dtbinh/AntRobots_2.0/CAD_files/ArduinoMega.SLDPRT

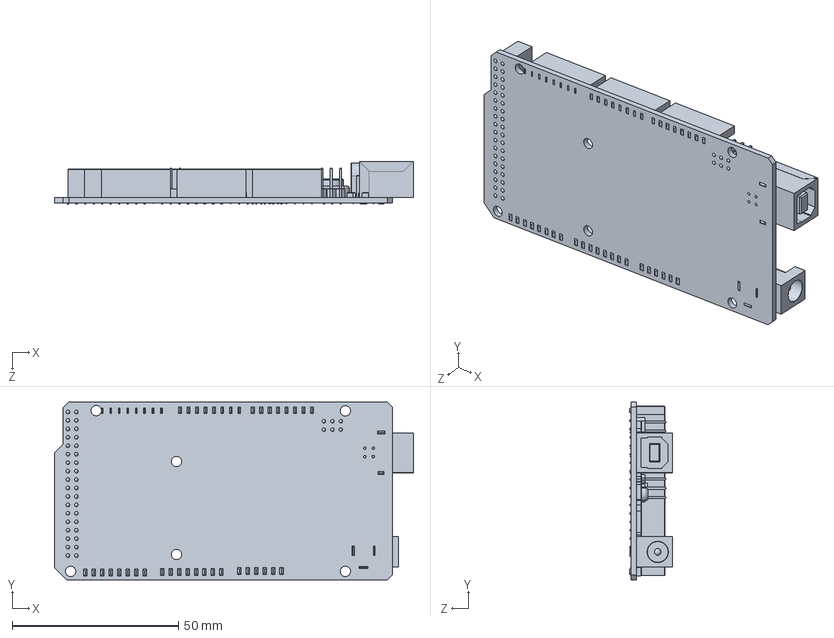
[picture p15: CAD file, 2016-06-14]
CAD_files/ArduinoMega.SLDPRT
107.9 x 53.4 x 13.0 mm
