dtbinh/AntRobots_2.0/CAD_files/micro claw base.SLDPRT

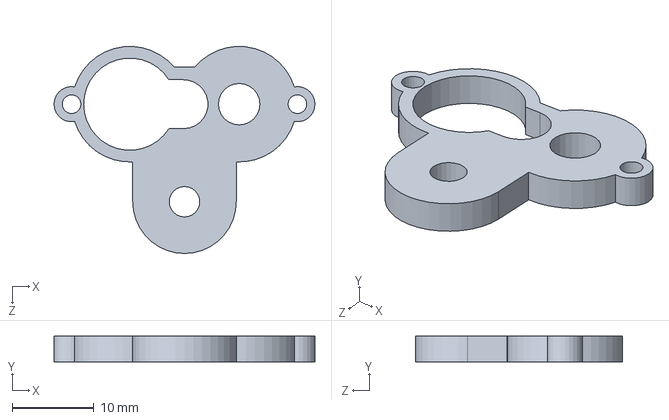
[picture p16: CAD file, 2016-06-14]
CAD_files/micro claw base.SLDPRT
32.0 x 3.17 x 25.4 mm
