dtbinh/AntRobots_2.0/CAD_files/new_ee_holder.SLDPRT

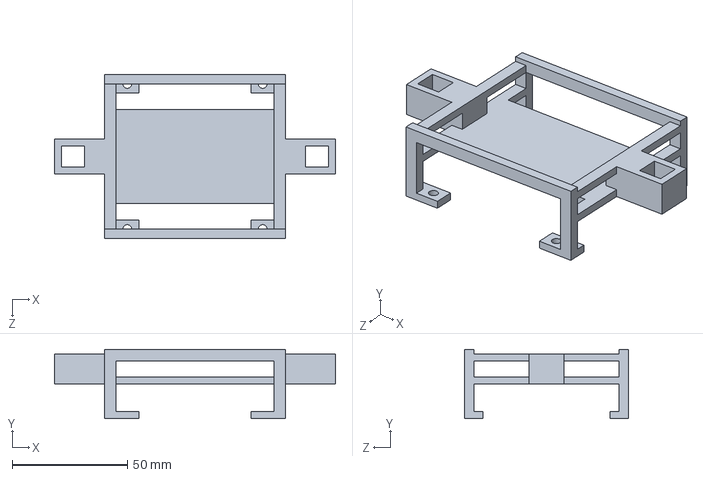
[picture p17: CAD file, 2016-06-14]
CAD_files/new_ee_holder.SLDPRT
122.0 x 30.0 x 71.0 mm
