dtbinh/AntRobots_2.0/CAD_files/pixy_lens.SLDPRT

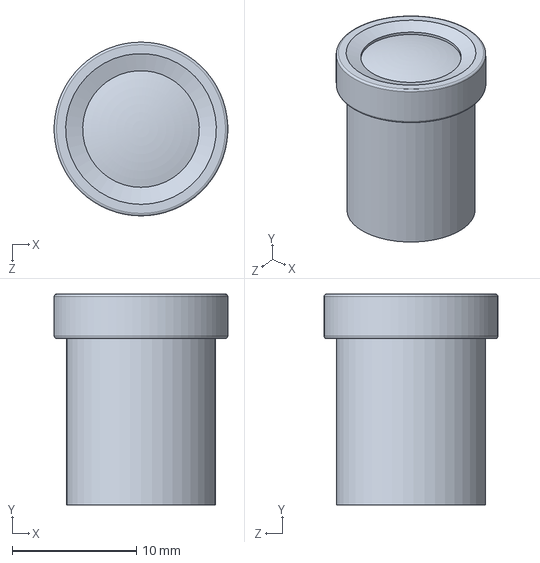
[picture p18: CAD file, 2016-06-14]
CAD_files/pixy_lens.SLDPRT
14.0 x 17.0 x 14.0 mm
