dtbinh/AntRobots_2.0/CAD_files/front mount.SLDPRT

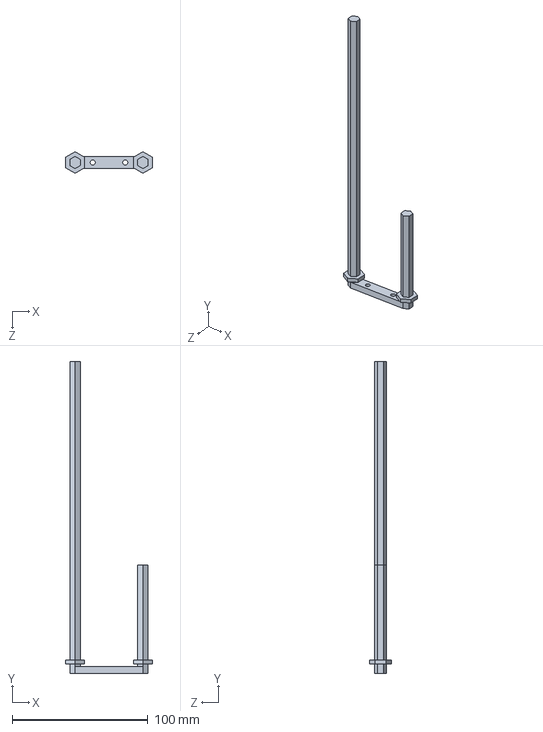
[picture p19: CAD file, 2016-06-14]
CAD_files/front mount.SLDPRT
63.8 x 230.0 x 15.9 mm
