dtbinh/AntRobots_2.0/CAD_files/front caster holder.SLDPRT

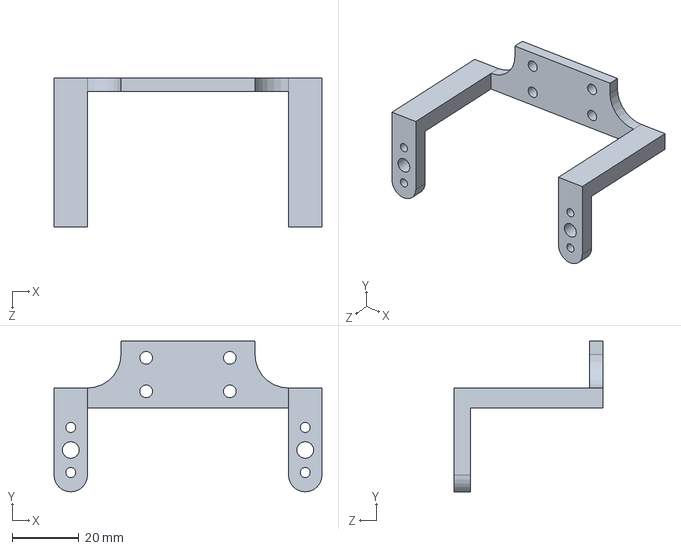
[picture p20: CAD file, 2016-06-14]
CAD_files/front caster holder.SLDPRT
80.0 x 45.0 x 44.5 mm
