dtbinh/AntRobots_2.0/CAD_files/switch-FSMRA6JH.SLDPRT

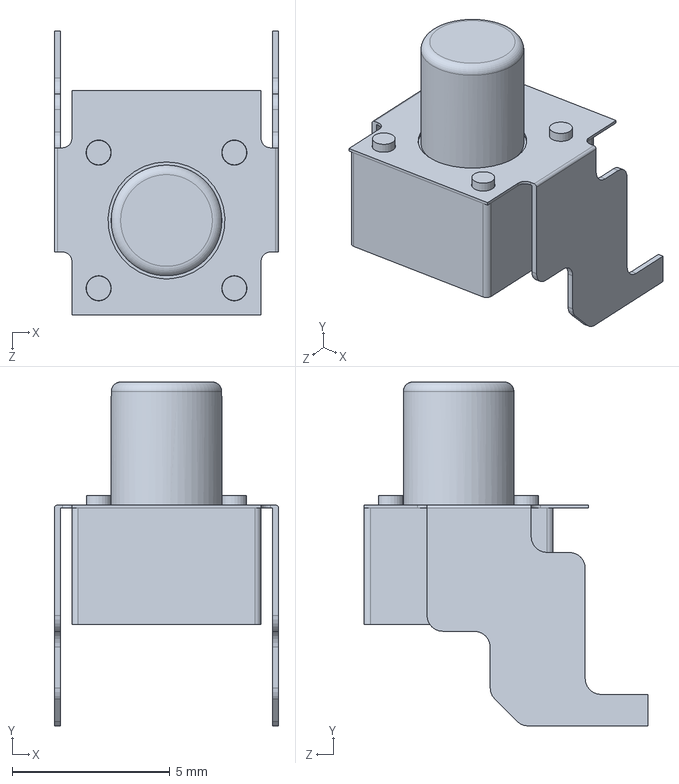
[picture p21: CAD file, 2016-06-14]
CAD_files/switch-FSMRA6JH.SLDPRT
7.11 x 10.9 x 8.99 mm
