dtbinh/AntRobots_2.0/CAD_files/Metal Ball Caster.SLDPRT

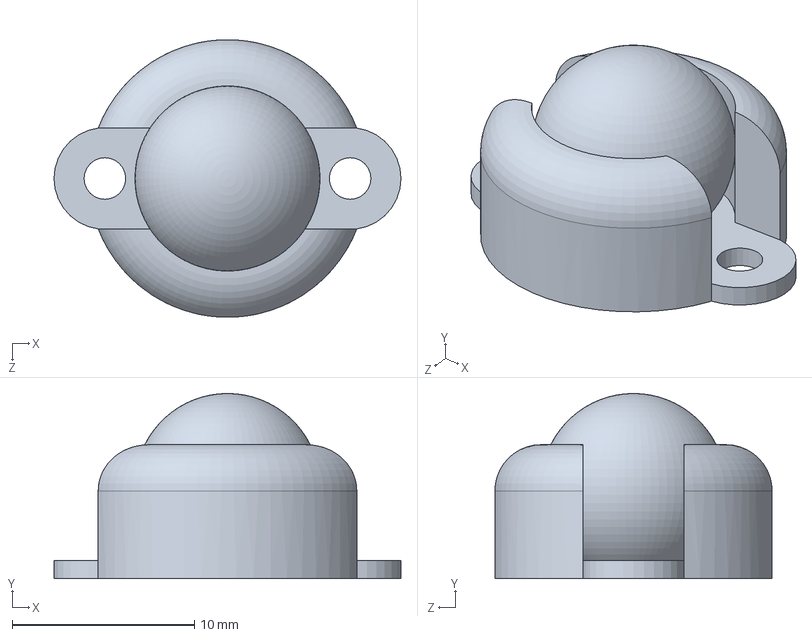
[picture p22: CAD file, 2016-06-14]
CAD_files/Metal Ball Caster.SLDPRT
19.1 x 10.2 x 15.2 mm
