dtbinh/AntRobots_2.0/CAD_files/Pixy_board.SLDPRT

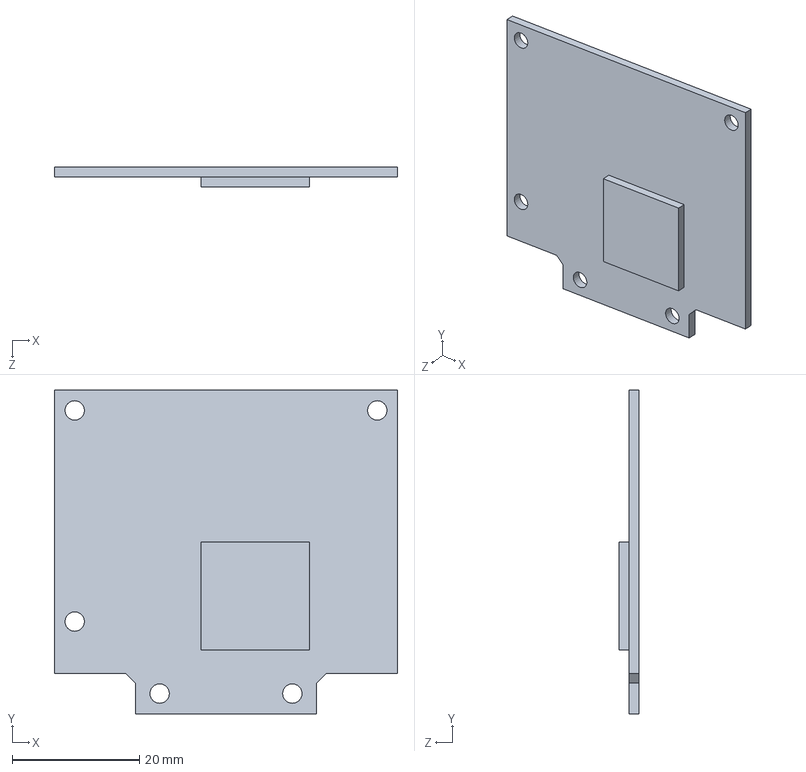
[picture p23: CAD file, 2016-06-14]
CAD_files/Pixy_board.SLDPRT
53.8 x 50.8 x 3.20 mm
