dtbinh/AntRobots_2.0/CAD_files/elecHolder.SLDPRT

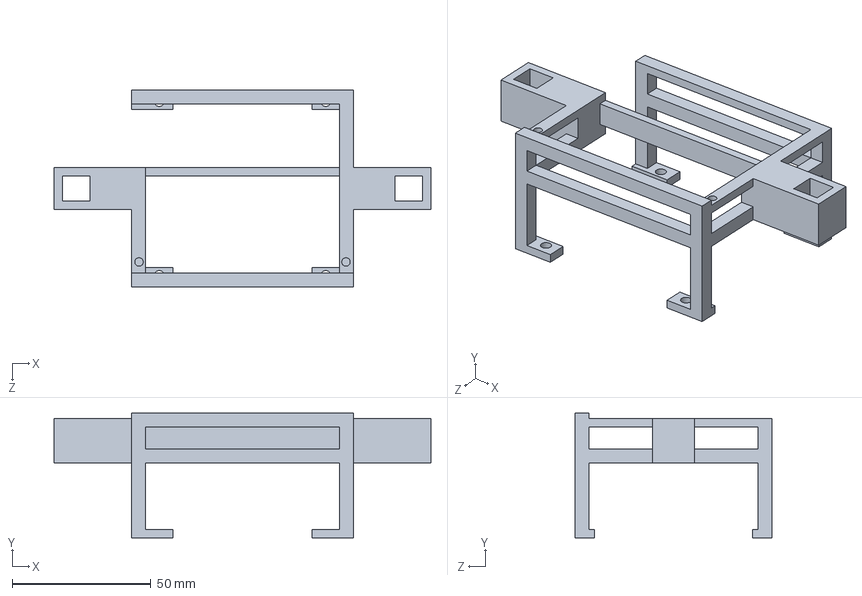
[picture p24: CAD file, 2016-06-14]
CAD_files/elecHolder.SLDPRT
136.0 x 45.0 x 71.0 mm
