dtbinh/AntRobots_2.0/CAD_files/Part2.SLDPRT

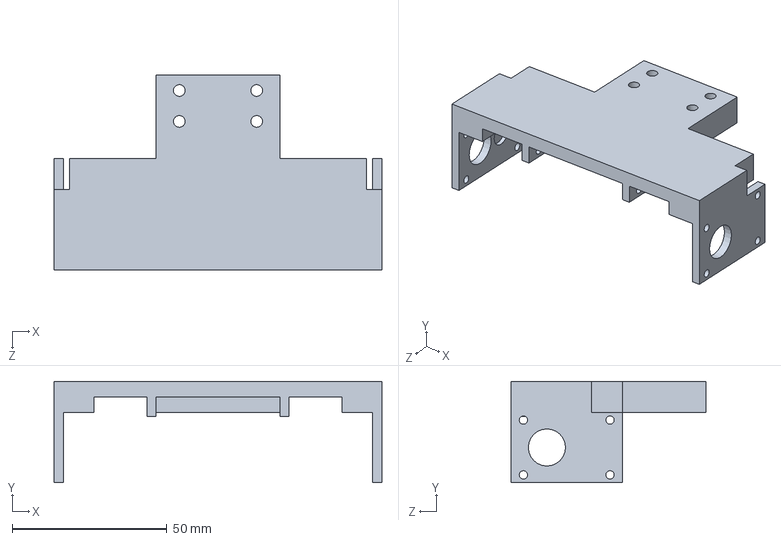
[picture p25: CAD file, 2016-06-14]
CAD_files/Part2.SLDPRT
106.0 x 32.6 x 63.0 mm
