dtbinh/AntRobots_2.0/CAD_files/M12_lens_holder.SLDPRT

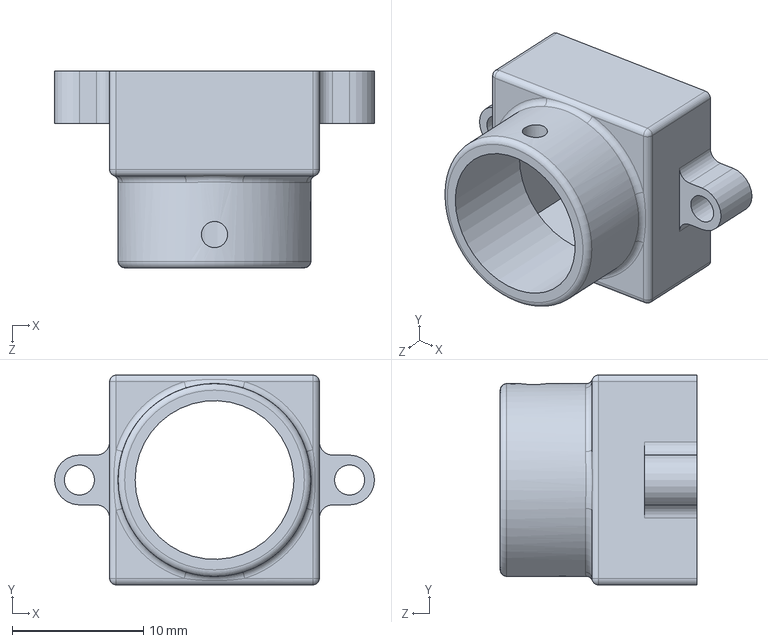
[picture p26: CAD file, 2016-06-14]
CAD_files/M12_lens_holder.SLDPRT
24.4 x 16.0 x 15.0 mm
