dtbinh/AntRobots_2.0/CAD_files/new side adapter.SLDPRT

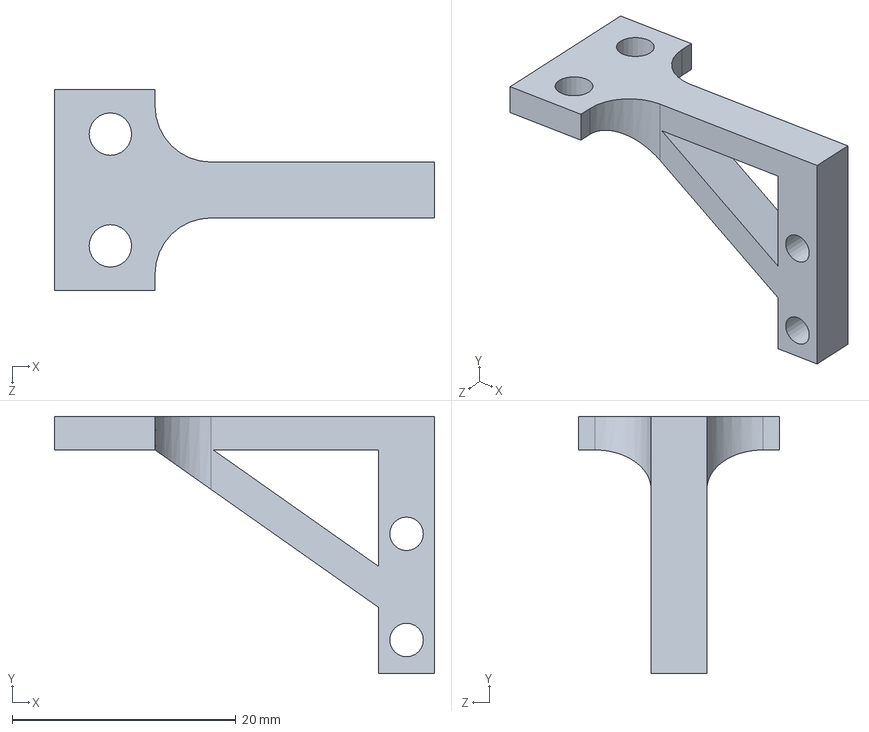
[picture p27: CAD file, 2016-06-14]
CAD_files/new side adapter.SLDPRT
34.0 x 23.0 x 18.0 mm
