dtbinh/AntRobots_2.0/CAD_files/claw.SLDPRT

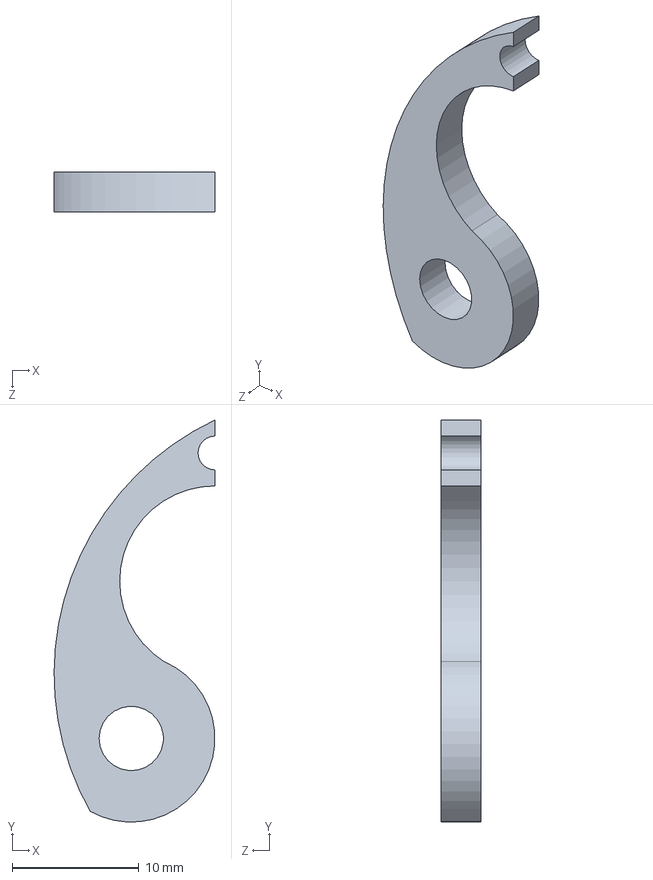
[picture p28: CAD file, 2016-06-14]
CAD_files/claw.SLDPRT
12.7 x 31.7 x 3.17 mm
