dtbinh/AntRobots_2.0/CAD_files/whisker mount.SLDPRT

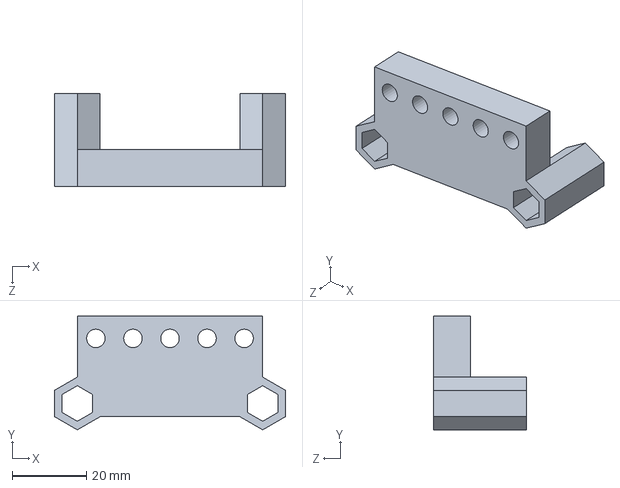
[picture p29: CAD file, 2016-06-14]
CAD_files/whisker mount.SLDPRT
62.3 x 30.7 x 25.0 mm
