dtbinh/AntRobots_2.0/CAD_files/header_MTA-100_2pins.SLDPRT

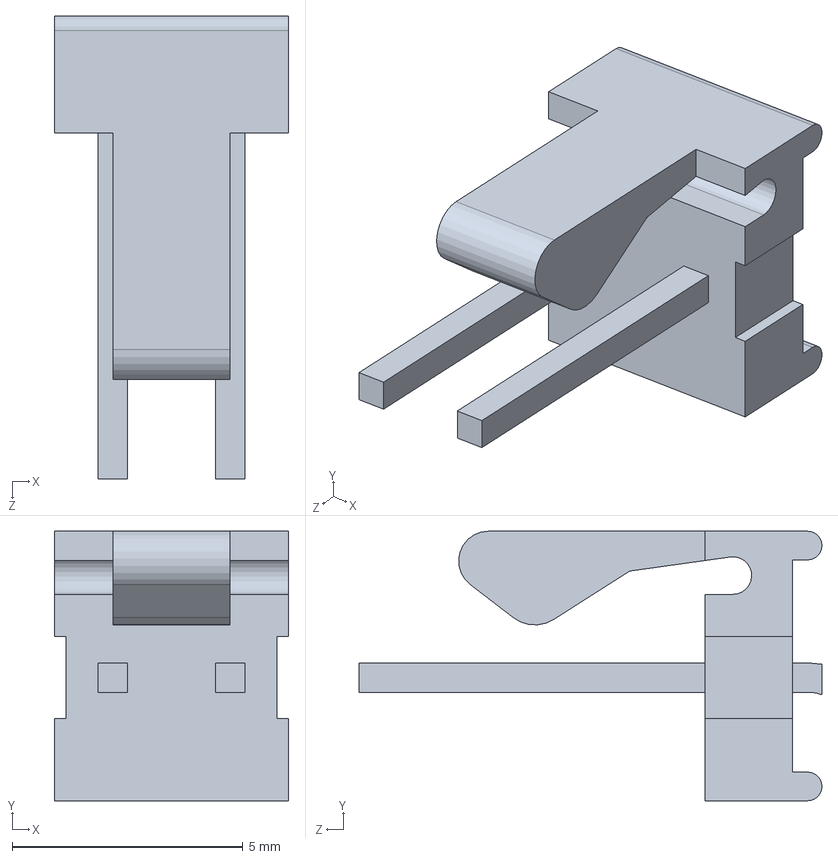
[picture p30: CAD file, 2016-06-14]
CAD_files/header_MTA-100_2pins.SLDPRT
5.08 x 5.84 x 10.0 mm
