dtbinh/AntRobots_2.0/CAD_files/ModularBodyBase.SLDPRT

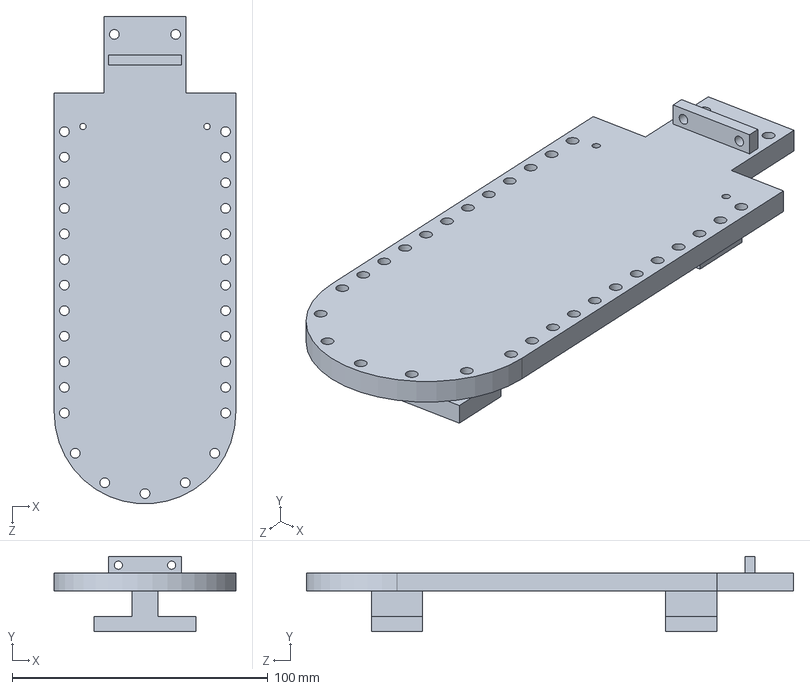
[picture p31: CAD file, 2016-06-14]
CAD_files/ModularBodyBase.SLDPRT
71.0 x 29.5 x 190.4 mm
