dtbinh/AntRobots_2.0/CAD_files/head mount spacer.SLDPRT

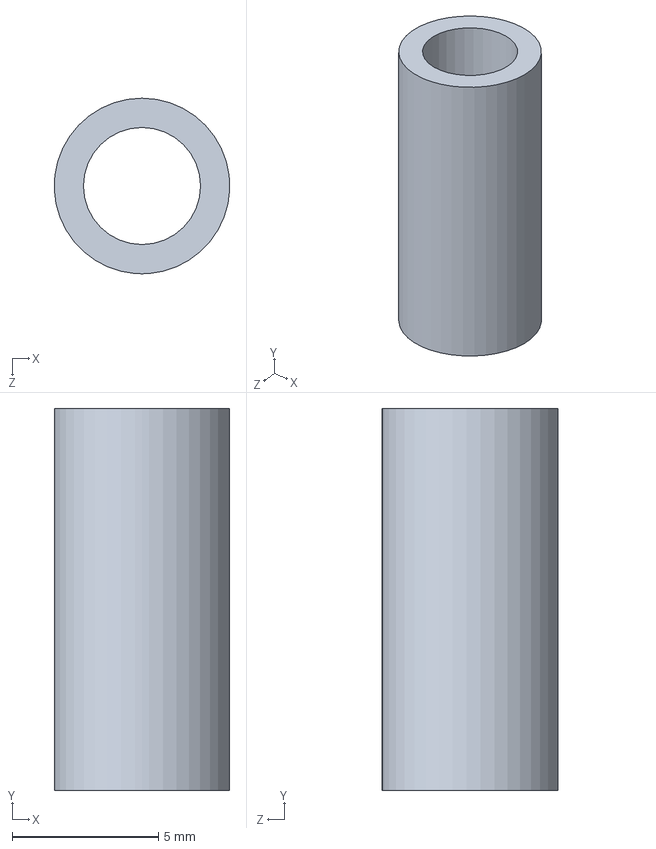
[picture p32: CAD file, 2016-06-14]
CAD_files/head mount spacer.SLDPRT
6.00 x 13.1 x 6.00 mm
