dtbinh/AntRobots_2.0/CAD_files/arm mount.SLDPRT

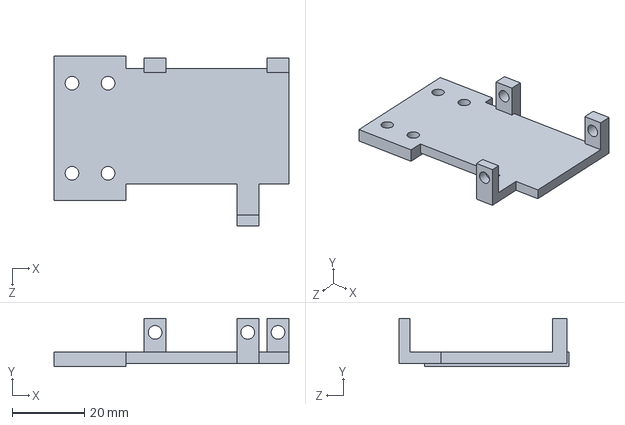
[picture p33: CAD file, 2016-06-14]
CAD_files/arm mount.SLDPRT
65.2 x 13.4 x 47.1 mm
