dtbinh/AntRobots_2.0/CAD_files/dummy battery.SLDPRT

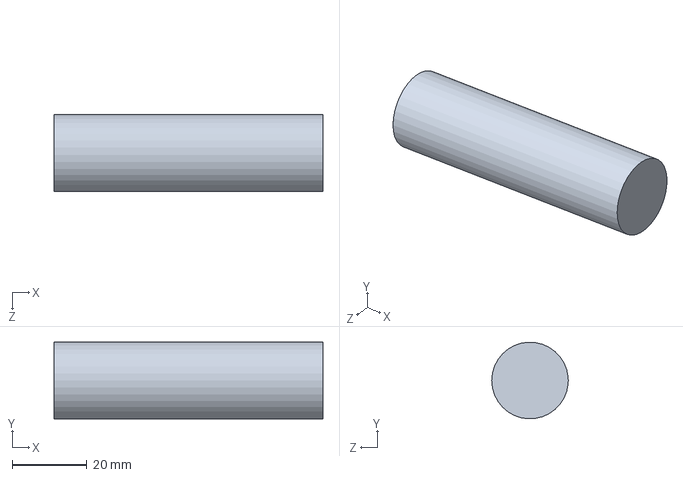
[picture p34: CAD file, 2016-06-14]
CAD_files/dummy battery.SLDPRT
72.0 x 20.5 x 20.5 mm
