dtbinh/AntRobots_2.0/CAD_files/quickIMU.SLDPRT

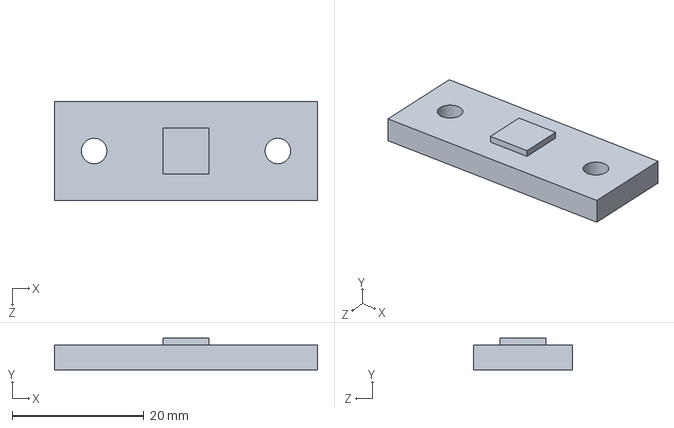
[picture p35: CAD file, 2016-06-14]
CAD_files/quickIMU.SLDPRT
40.0 x 4.80 x 15.0 mm
