dtbinh/AntRobots_2.0/CAD_files/batHolder.SLDPRT

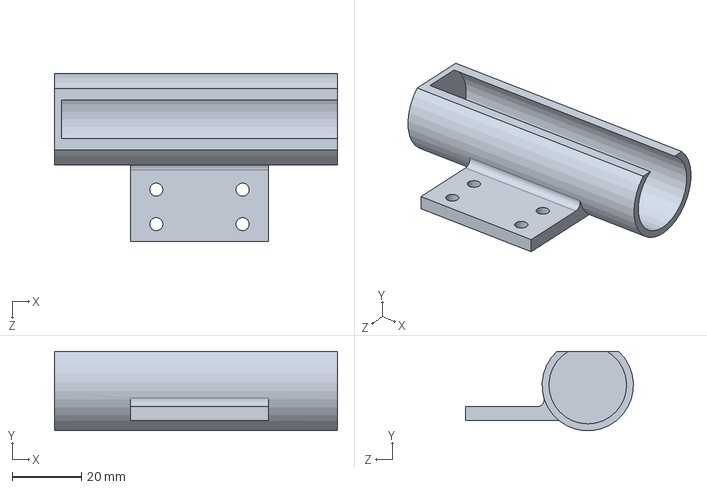
[picture p36: CAD file, 2016-06-14]
CAD_files/batHolder.SLDPRT
82.0 x 22.9 x 48.6 mm
