dtbinh/AntRobots_2.0/CAD_files/quick_switch.SLDPRT

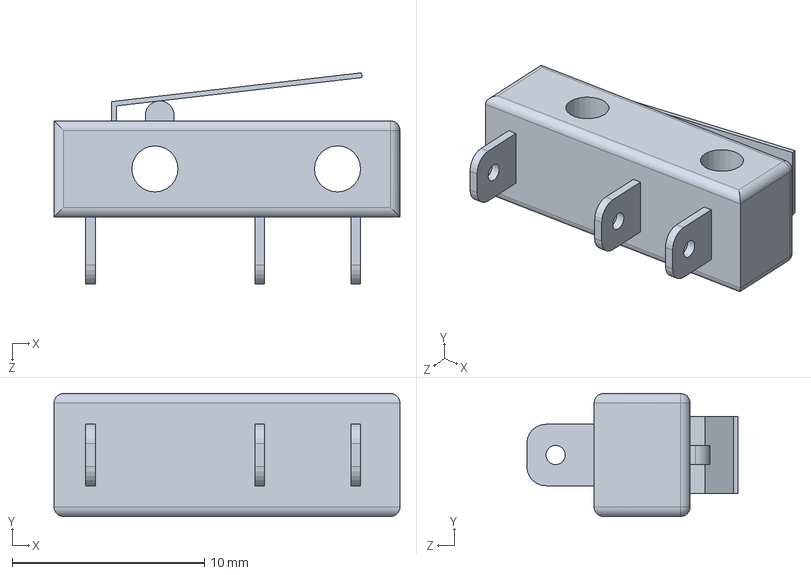
[picture p37: CAD file, 2016-06-14]
CAD_files/quick_switch.SLDPRT
18.0 x 6.40 x 11.0 mm
