dtbinh/AntRobots_2.0/CAD_files/IR Sensor.SLDPRT

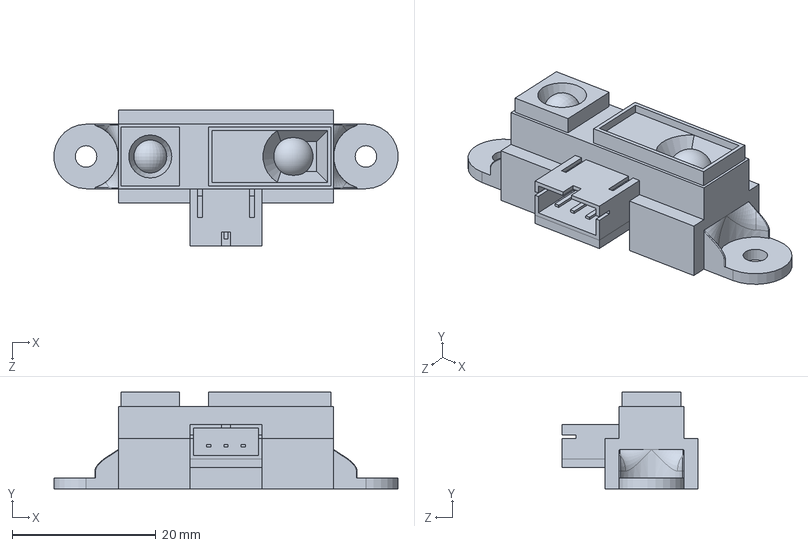
[picture p38: CAD file, 2016-06-14]
CAD_files/IR Sensor.SLDPRT
47.9 x 13.5 x 19.0 mm
