dtbinh/AntRobots_2.0/CAD_files/HS-55.SLDPRT

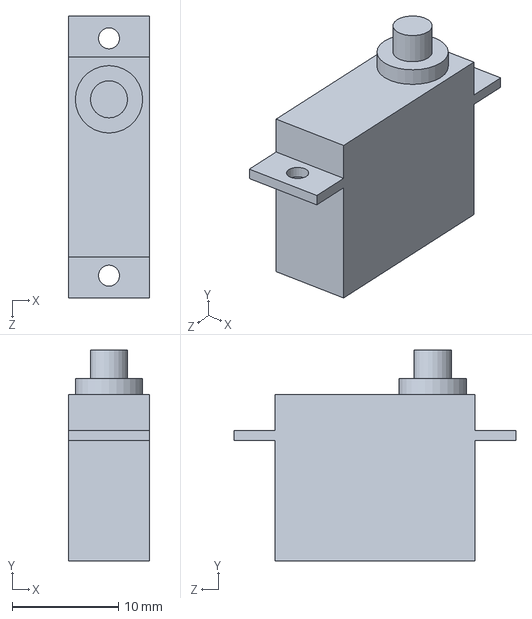
[picture p39: CAD file, 2016-06-14]
CAD_files/HS-55.SLDPRT
7.62 x 19.9 x 26.6 mm
