dtbinh/AntRobots_2.0/CAD_files/gyro extention.SLDPRT

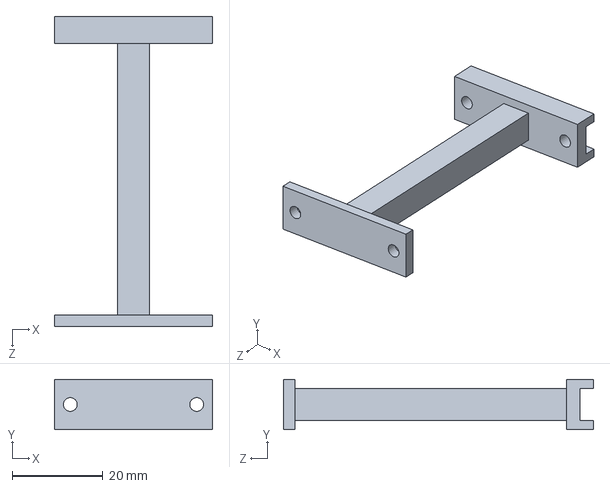
[picture p40: CAD file, 2016-06-14]
CAD_files/gyro extention.SLDPRT
35.0 x 11.1 x 68.5 mm
