dtbinh/AntRobots_2.0/CAD_files/gripper servo holder.SLDPRT

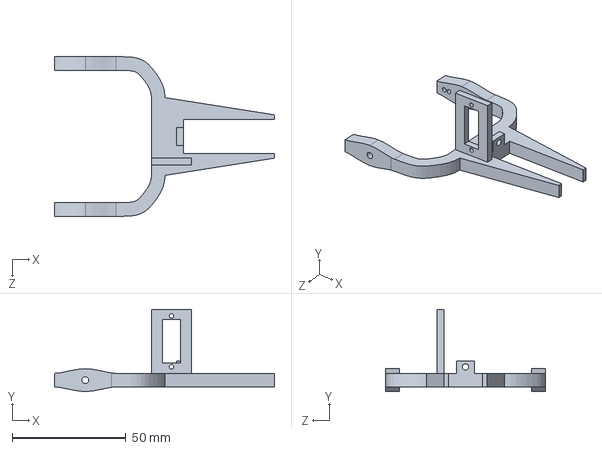
[picture p41: CAD file, 2016-06-14]
CAD_files/gripper servo holder.SLDPRT
96.5 x 36.0 x 70.1 mm
