dtbinh/AntRobots_2.0/CAD_files/new side adapter back.SLDPRT

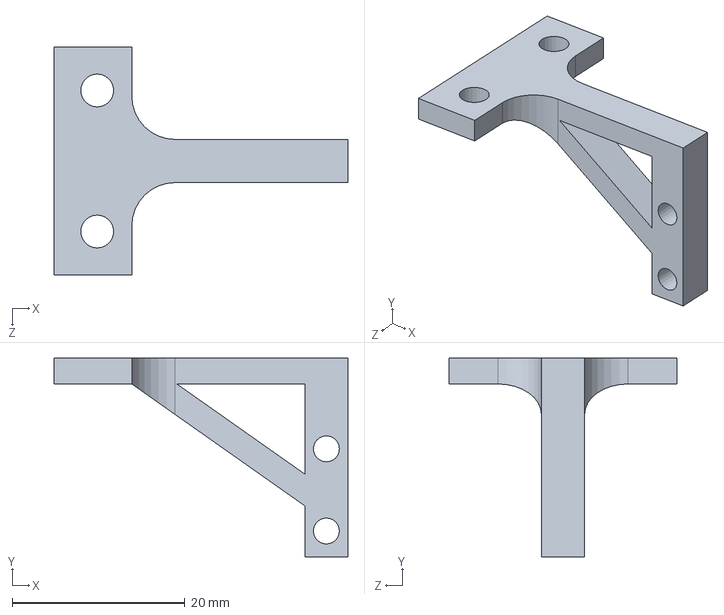
[picture p42: CAD file, 2016-06-14]
CAD_files/new side adapter back.SLDPRT
34.0 x 23.0 x 26.4 mm
