dtbinh/AntRobots_2.0/CAD_files/quick_switch2.SLDPRT

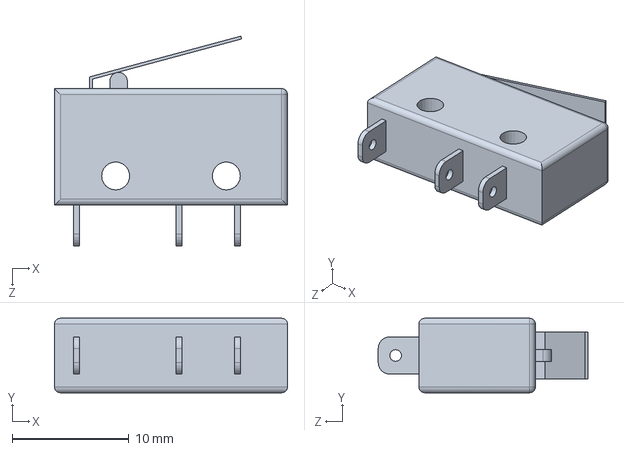
[picture p43: CAD file, 2016-06-14]
CAD_files/quick_switch2.SLDPRT
20.0 x 6.40 x 18.0 mm
