dtbinh/AntRobots_2.0/CAD_files/RGB_led_CMS.SLDPRT

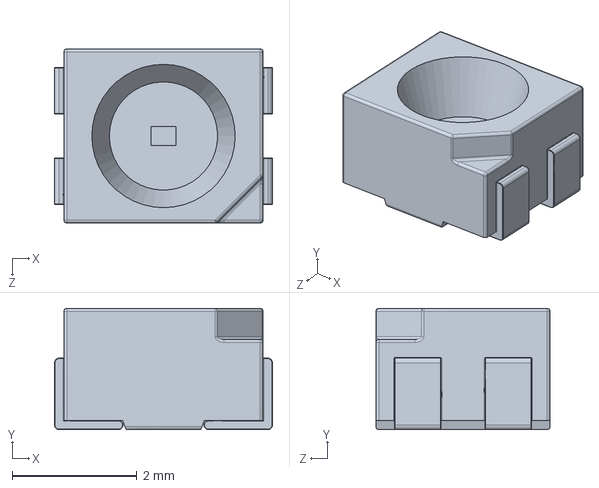
[picture p44: CAD file, 2016-06-14]
CAD_files/RGB_led_CMS.SLDPRT
3.50 x 1.95 x 2.80 mm
