dtbinh/AntRobots_2.0/CAD_files/header_2x5ways.SLDPRT

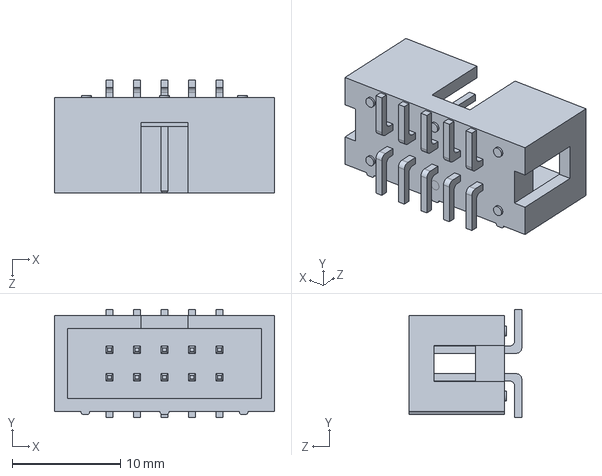
[picture p45: CAD file, 2016-06-14]
CAD_files/header_2x5ways.SLDPRT
20.3 x 10.0 x 10.4 mm
